MadRobin13/Muse/src/test_mouse.cpp

// #include <BleMouse.h>
// #include <HardwareSerial.h>

// BleMouse bleMouse;

// void setup() {
//   Serial.begin(115200);
//   bleMouse.begin();
// }

// void loop() {
//   if(bleMouse.isConnected()) {
//     bleMouse.move(10, 0); // Move mouse to the right
//     delay(1000);
//     bleMouse.move(-10, 0); // Move mouse to the left
//     delay(1000);
//   }
// }
